gyarab/3D_Printer/3D_modely/extruder/E drzace vetracku.stl

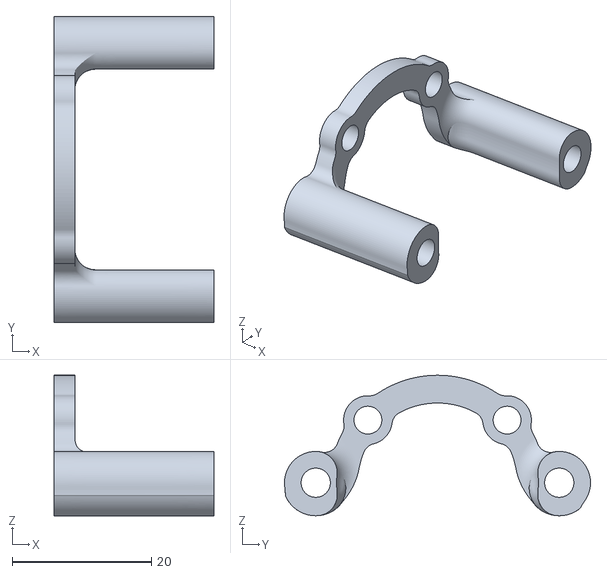
[picture p36: CAD file, 2020-04-11]
3D_modely/extruder/E drzace vetracku.stl
23.0 x 44.0 x 20.2
