gyarab/3D_Printer/3D_modely/osa Y/drzak motorku.stl

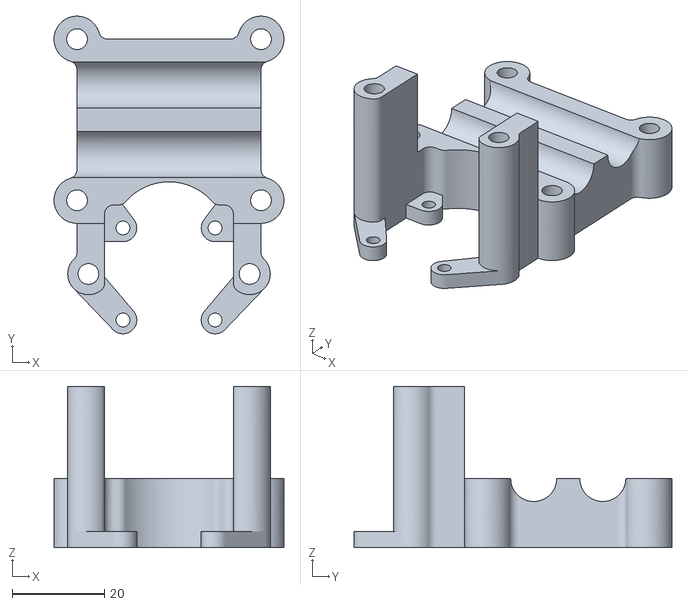
[picture p37: CAD file, 2020-04-11]
3D_modely/osa Y/drzak motorku.stl
50.0 x 69.0 x 35.0
