gyarab/3D_Printer/3D_modely/osa Z/drzak zavitovych tyci.stl

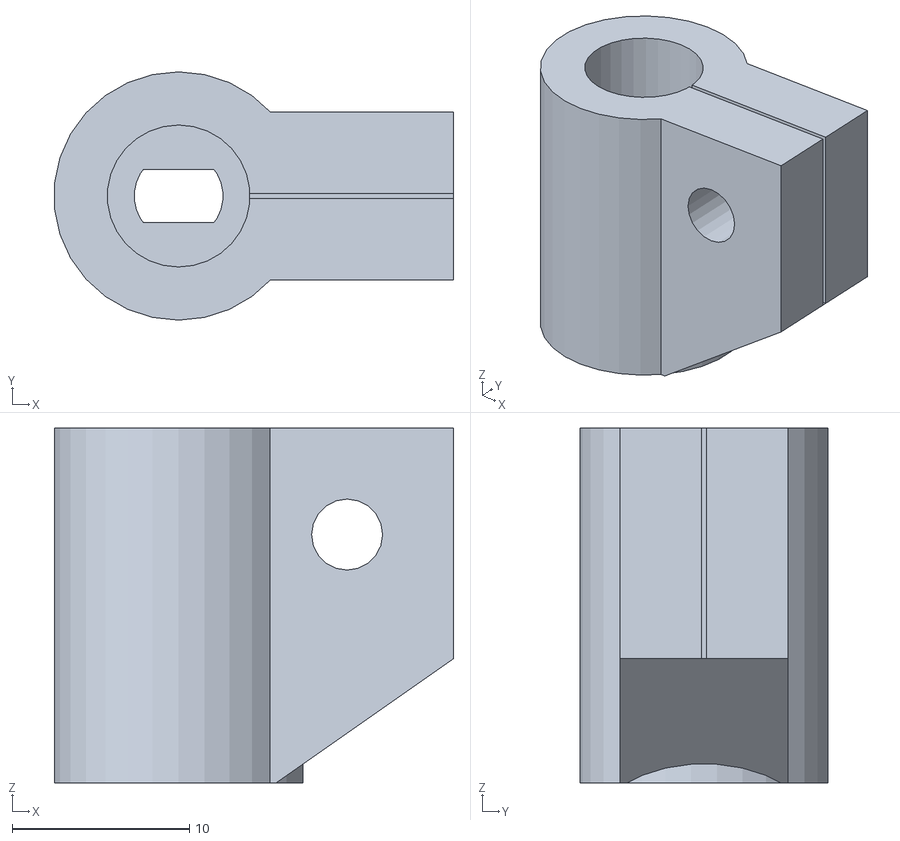
[picture p38: CAD file, 2020-04-11]
3D_modely/osa Z/drzak zavitovych tyci.stl
22.5 x 14.0 x 20.0
