gyarab/3D_Printer/3D_modely/rám/spodní rám a.stl

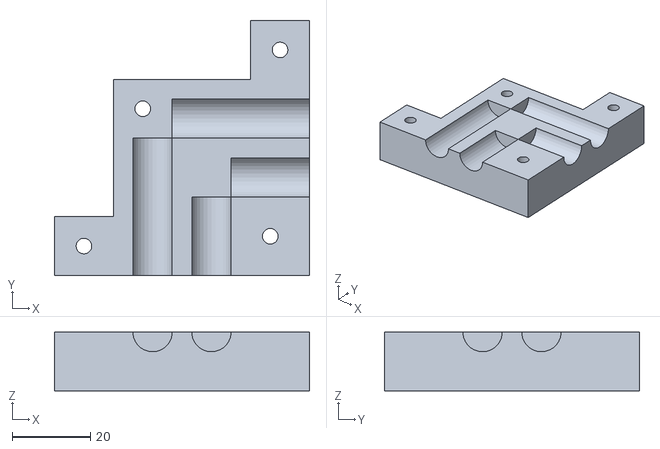
[picture p39: CAD file, 2020-04-11]
3D_modely/rám/spodní rám a.stl
65.0 x 65.0 x 15.0
