gyarab/3D_Printer/3D_modely/extruder/zafixování pásů.stl

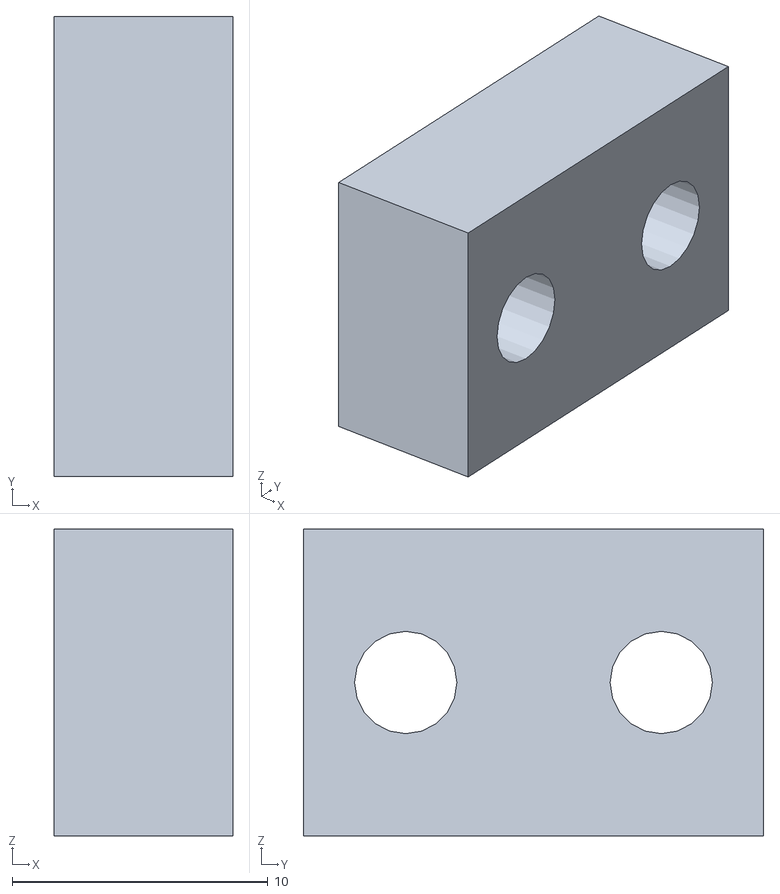
[picture p40: CAD file, 2020-04-11]
3D_modely/extruder/zafixování pásů.stl
7.00 x 18.0 x 12.0
