gyarab/3D_Printer/3D_modely/osa Y/drzak motorku2.stl

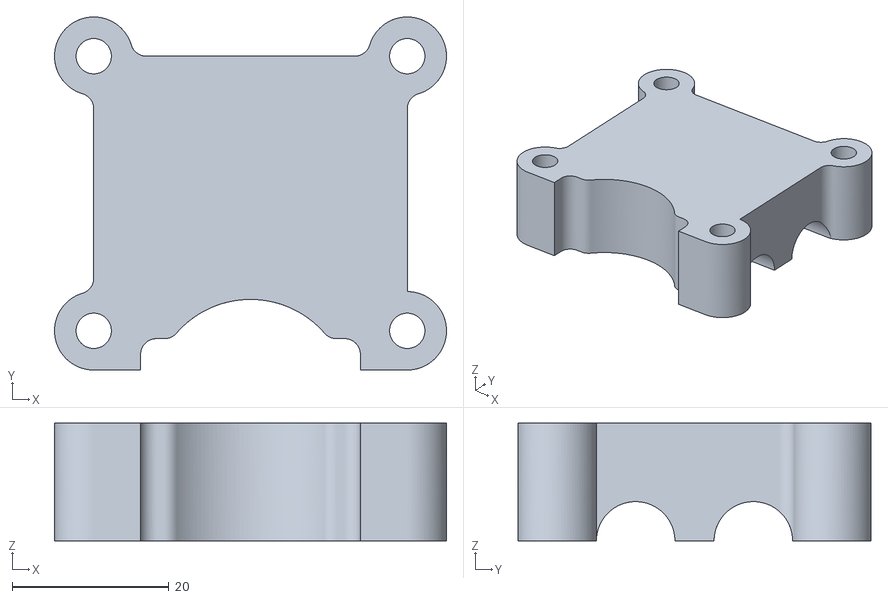
[picture p41: CAD file, 2020-04-11]
3D_modely/osa Y/drzak motorku2.stl
50.0 x 45.0 x 15.0
