gyarab/3D_Printer/3D_modely/osa Z/Upevnění vertikálních motorů 1.stl

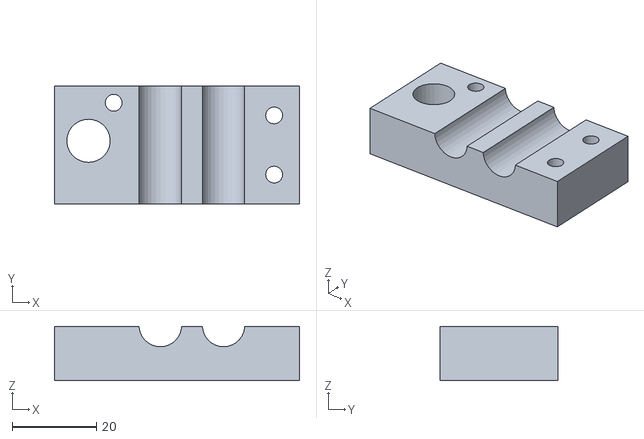
[picture p42: CAD file, 2020-04-11]
3D_modely/osa Z/Upevnění vertikálních motorů 1.stl
58.0 x 28.0 x 12.8
