gyarab/3D_Printer/3D_modely/extruder/drzak vetracku hotendu.stl

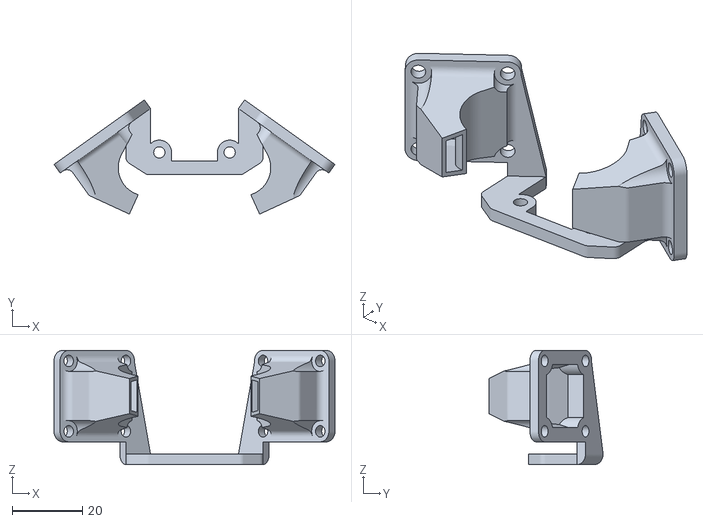
[picture p43: CAD file, 2020-04-11]
3D_modely/extruder/drzak vetracku hotendu.stl
79.9 x 32.5 x 32.5
