gyarab/3D_Printer/3D_modely/osa Y/drzak tyci2.stl

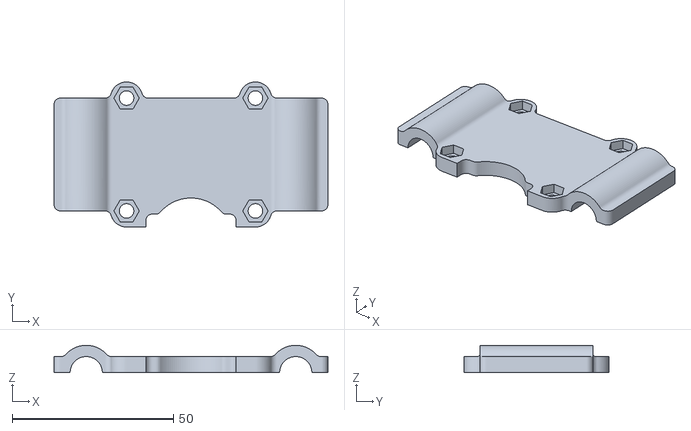
[picture p44: CAD file, 2020-04-11]
3D_modely/osa Y/drzak tyci2.stl
85.0 x 45.0 x 8.50
