gyarab/3D_Printer/3D_modely/osa Z/Upevnění vertikálních motorů 2.stl

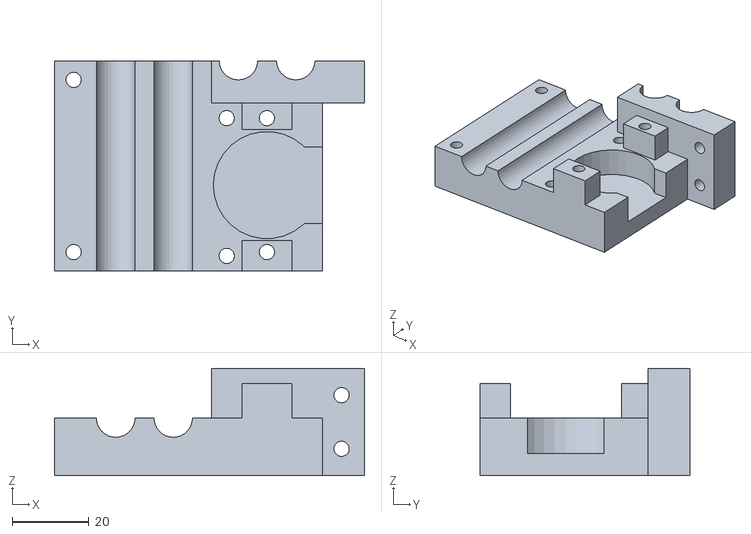
[picture p45: CAD file, 2020-04-11]
3D_modely/osa Z/Upevnění vertikálních motorů 2.stl
81.0 x 55.0 x 28.0
