gyarab/3D_Printer/3D_modely/extruder/drzak indukcniho spinace.stl

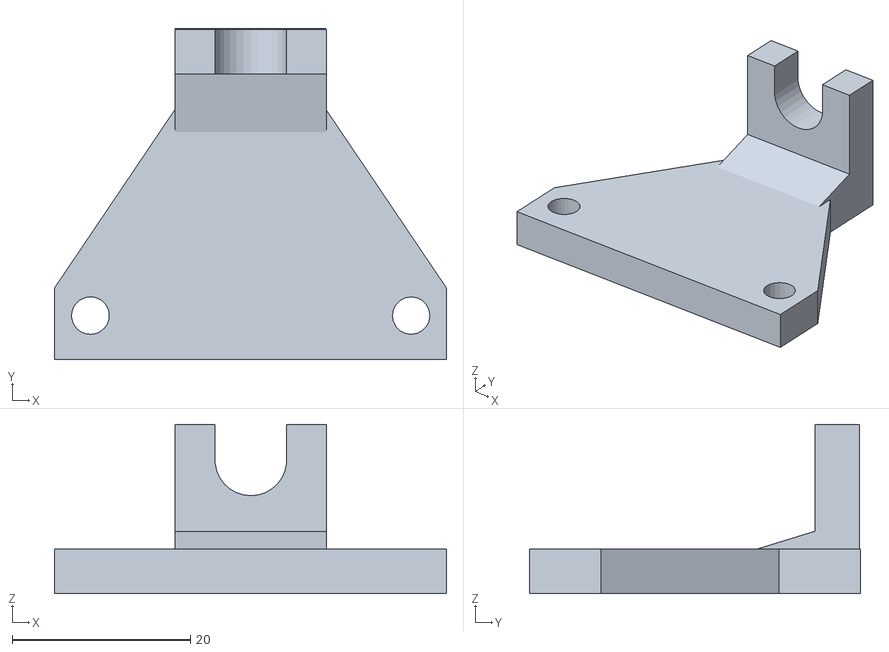
[picture p46: CAD file, 2020-04-11]
3D_modely/extruder/drzak indukcniho spinace.stl
44.0 x 37.1 x 19.0
