gyarab/3D_Printer/3D_modely/extruder/drzak lineárnich ložisek 2.stl

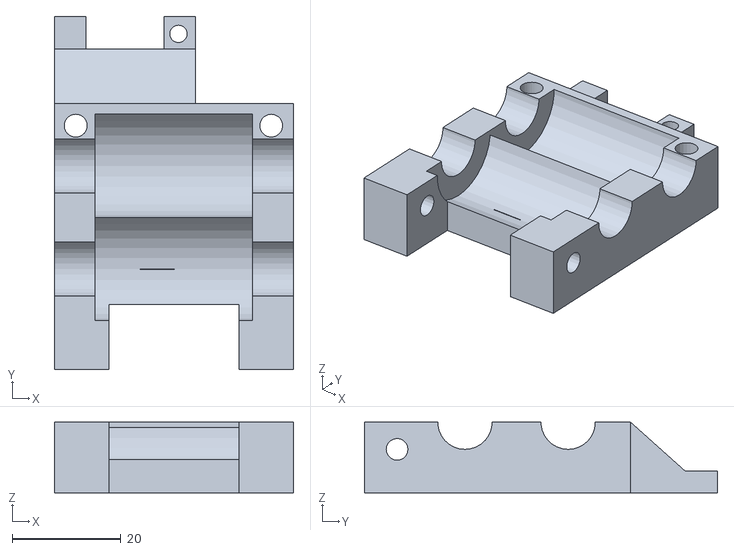
[picture p47: CAD file, 2020-04-11]
3D_modely/extruder/drzak lineárnich ložisek 2.stl
44.0 x 65.0 x 13.0
