gyarab/3D_Printer/3D_modely/extruder/extruder 1.stl

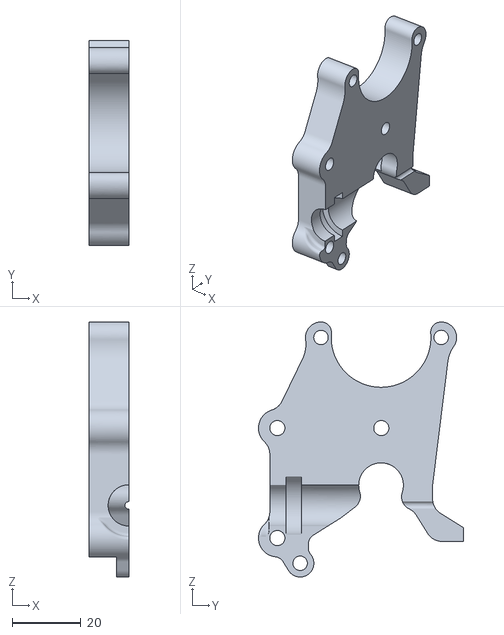
[picture p48: CAD file, 2020-04-11]
3D_modely/extruder/extruder 1.stl
11.5 x 59.7 x 74.2
