gyarab/3D_Printer/3D_modely/extruder/extruder2.stl

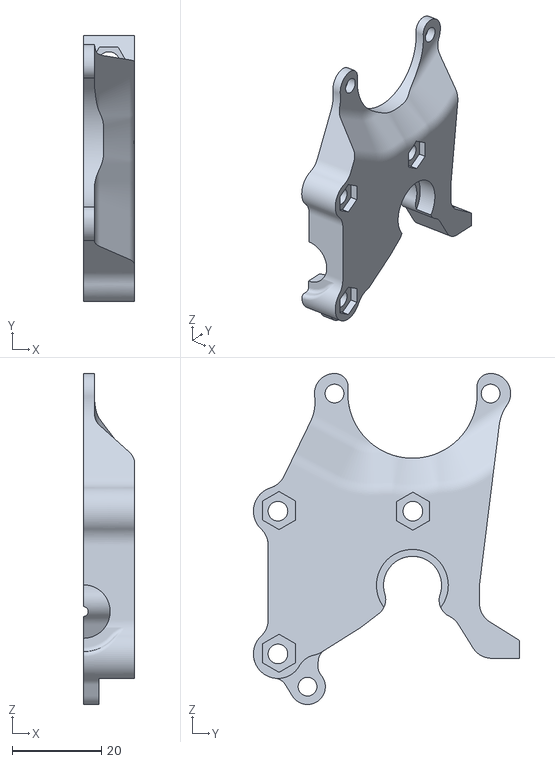
[picture p49: CAD file, 2020-04-11]
3D_modely/extruder/extruder2.stl
11.5 x 59.7 x 74.2
