gyarab/3D_Printer/3D_modely/extruder/drzak lineárnich ložisek.stl

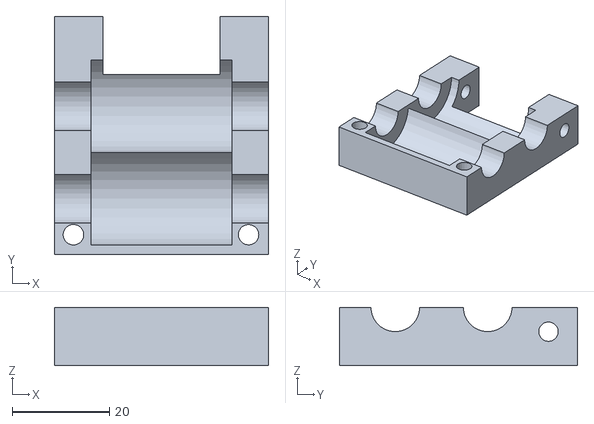
[picture p50: CAD file, 2020-04-11]
3D_modely/extruder/drzak lineárnich ložisek.stl
44.0 x 49.0 x 12.0
