gyarab/3D_Printer/3D_modely/extruder/Spur Gear (36 teeth).stl

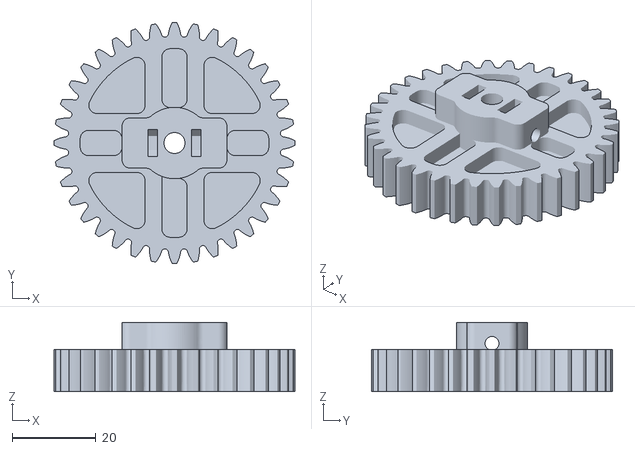
[picture p51: CAD file, 2020-04-11]
3D_modely/extruder/Spur Gear (36 teeth).stl
57.4 x 57.4 x 16.5
